ItabirAr/CITinova-Rede_de_Sensores/CASE/Case v2/Imagens/Case_v2_impressa_6.jpg

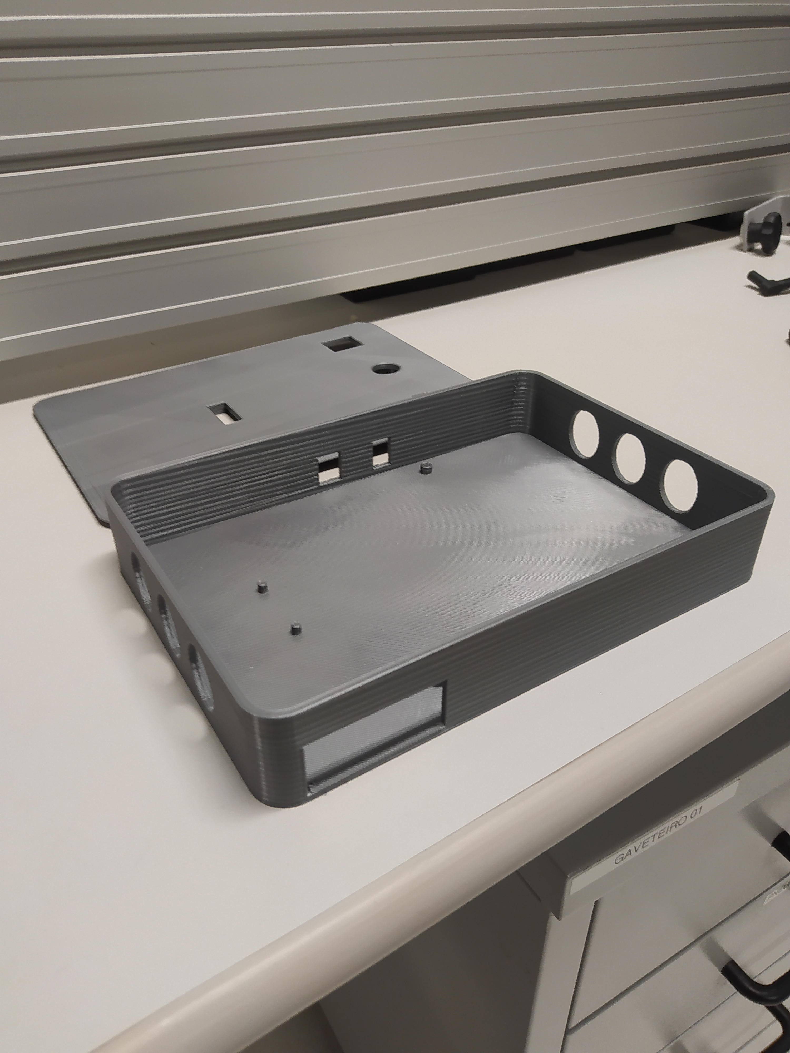
CASE/Case v2/Imagens/Case_v2_impressa_6.jpg
