ItabirAr/CITinova-Rede_de_Sensores/PMS5003/Códigos/codigoPMS5003_lib2/codigoPMS5003_lib2.ino

//Esse código utiliza a biblioteca "PMS_Library-1.1.0"

#include "PMS.h"

PMS pms(Serial);
PMS::DATA data;

void setup()
{
  Serial.begin(9600);   // GPIO1, GPIO3 (TX/RX pin on ESP-12E Development Board)
  Serial1.begin(9600);  // GPIO2 (D4 pin on ESP-12E Development Board)
}

void loop()
{
  if (pms.read(data))
  {
    Serial1.print("PM 1.0 (ug/m3): ");
    Serial1.println(data.PM_AE_UG_1_0);

    Serial1.print("PM 2.5 (ug/m3): ");
    Serial1.println(data.PM_AE_UG_2_5);

    Serial1.print("PM 10.0 (ug/m3): ");
    Serial1.println(data.PM_AE_UG_10_0);

    Serial1.println();
  }

}
